gorry/p8kbto88/kicad/p8kbto88.kicad_sch

## KiCad design kicad/p8kbto88.kicad_sch (2024-07-19)

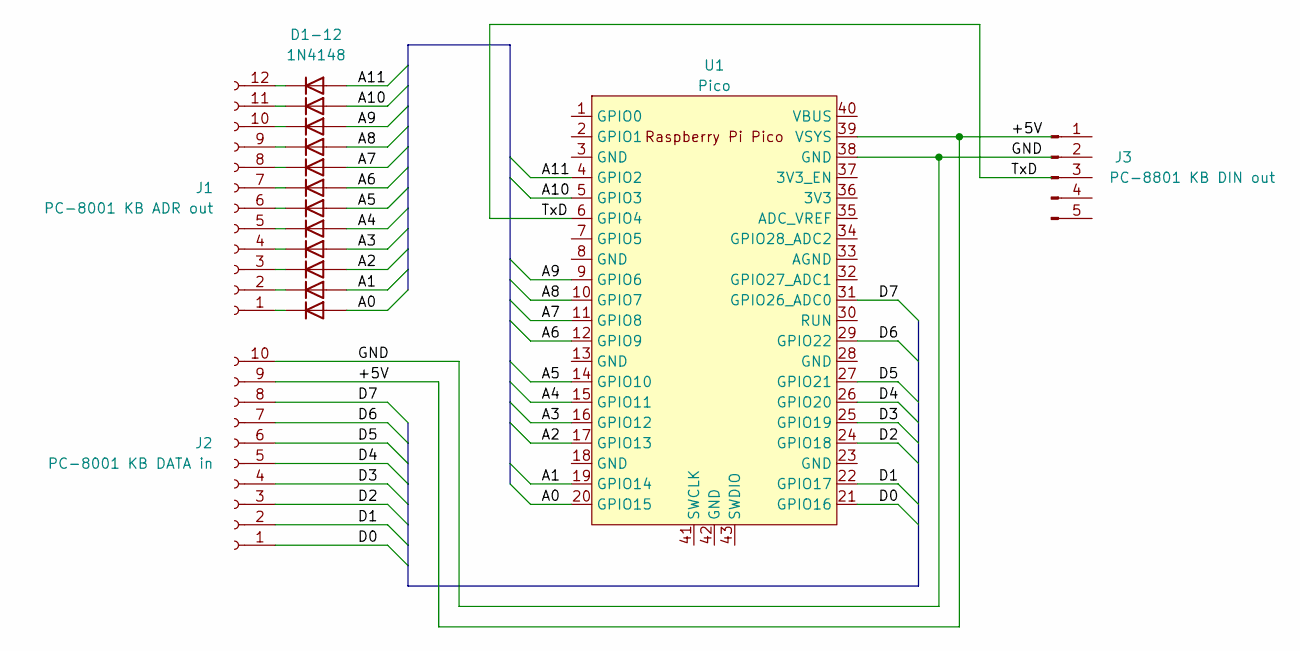
[picture p3: schematic p8kbto88.kicad_sch]

Parts:
D1, D1-12, D2, D3, D4, D5, D6, D7, D8, D9, D10, D11: 1N4148; D_DO-35_SOD27_P7.62mm_Horizontal
J1: PC-8001 KB ADR out
J2: PC-8001 KB DATA in
J3: PC-8801 KB DIN out
U1: Pico; RPi_Pico_SMD_TH

Connections:
+5V: J2.9, U1.39 (VSYS)
A0: D1.2 (A), U1.20 (GPIO15)
A1: D2.2 (A), U1.19 (GPIO14)
A2: D3.2 (A), U1.17 (GPIO13)
A3: D4.2 (A), U1.16 (GPIO12)
A4: D5.2 (A), U1.15 (GPIO11)
A5: D6.2 (A), U1.14 (GPIO10)
A6: D7.2 (A), U1.12 (GPIO9)
A7: D8.2 (A), U1.11 (GPIO8)
A8: D9.2 (A), U1.10 (GPIO7)
A9: D10.2 (A), U1.9 (GPIO6)
A10: D11.2 (A), U1.5 (GPIO3)
A11: D1-12.2 (A), U1.4 (GPIO2)
D0: J2.1, U1.21 (GPIO16)
D1: J2.2, U1.22 (GPIO17)
D2: J2.3, U1.24 (GPIO18)
D3: J2.4, U1.25 (GPIO19)
D4: J2.5, U1.26 (GPIO20)
D5: J2.6, U1.27 (GPIO21)
D6: J2.7, U1.29 (GPIO22)
D7: J2.8, U1.31 (GPIO26_ADC0)
GND: J2.10, U1.38 (GND)
unnamed: D1-12.1 (K), J1.12
unnamed: D1.1 (K), J1.1
unnamed: D2.1 (K), J1.2
unnamed: D3.1 (K), J1.3
unnamed: D4.1 (K), J1.4
unnamed: D5.1 (K), J1.5
unnamed: D6.1 (K), J1.6
unnamed: D7.1 (K), J1.7
unnamed: D8.1 (K), J1.8
unnamed: D9.1 (K), J1.9
unnamed: D10.1 (K), J1.10
unnamed: D11.1 (K), J1.11
TxD: U1.6 (GPIO4)
